1kbgz/linerack/hardware/mechanical/old/v0-m4/linerack-enclosure-m4-lid.stl

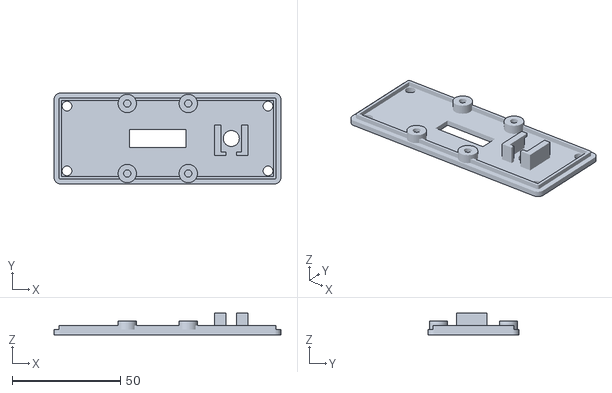
[picture p15: CAD file, 2026-08-30, an earlier design]
hardware/mechanical/old/v0-m4/linerack-enclosure-m4-lid.stl
105.0 x 42.0 x 10.1
