1kbgz/linerack/hardware/mechanical/old/compact-23mm/linerack-enclosure-compact-base.stl

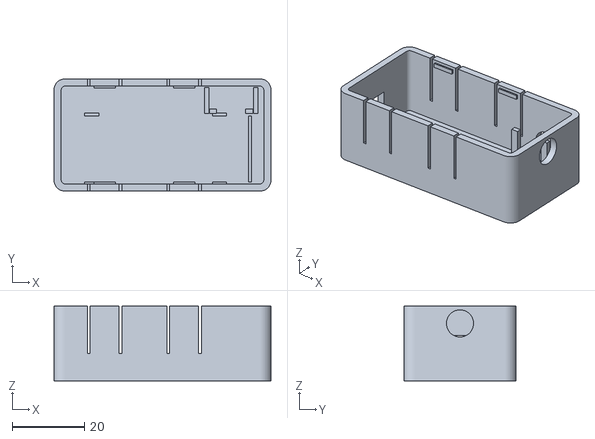
[picture p16: CAD file, 2026-08-30, an earlier design]
hardware/mechanical/old/compact-23mm/linerack-enclosure-compact-base.stl
60.0 x 31.0 x 20.6
